fbelavenuto/msxsdmapperv2/CPLD/src/sdmapper.vhd

--
-- Projeto MSX SD Mapper
--
-- Copyright (c) 2014
-- Fabio Belavenuto

-- This documentation describes Open Hardware and is licensed under the CERN OHL v. 1.1.
-- You may redistribute and modify this documentation under the terms of the
-- CERN OHL v.1.1. (http://ohwr.org/cernohl). This documentation is distributed
-- WITHOUT ANY EXPRESS OR IMPLIED WARRANTY, INCLUDING OF MERCHANTABILITY,
-- SATISFACTORY QUALITY AND FITNESS FOR A PARTICULAR PURPOSE.
-- Please see the CERN OHL v.1.1 for applicable conditions

-- Modulo TOP - implementa o controle da Megarom ASCII16 para o Nextor
-- HW version 2 - dropped Megaram to add HW timer

library ieee;
use ieee.std_logic_1164.all;
use ieee.numeric_std.all;

entity sdmapper is
	port(
		clock_i			: in    std_logic;
		reset_n_i		: in    std_logic;
		sw_i				: in    std_logic_vector( 1 downto 0);
		-- BUS interface
		addr_bus_i		: in    std_logic_vector(15 downto 0);
		data_bus_io		: inout std_logic_vector( 7 downto 0);
		wr_n_i			: in    std_logic;
		rd_n_i			: in    std_logic;
		iorq_n_i			: in    std_logic;
		m1_n_i			: in    std_logic;
		sltsl_n_i		: in    std_logic;
		busdir_n_o		: out   std_logic;
		wait_n_o			: out   std_logic;
		-- ROM interface
		rom_a_o			: out   std_logic_vector(17 downto 14);
		rom_ce_n_o		: out   std_logic;
		rom_we_n_o		: out   std_logic;
		-- RAM interface
		ram_a_o			: out   std_logic_vector(18 downto 13);
		ram_cs_n_o		: out   std_logic;
		ram_we_n_o		: out   std_logic;
		-- SD card interface
		sd_cs_n_o		: out   std_logic_vector( 1 downto 0);
		sd_sclk_o		: out   std_logic;
		sd_mosi_o		: out   std_logic;
		sd_miso_i		: in    std_logic;
		sd_wp_i			: in    std_logic_vector( 1 downto 0);		-- 1 = Write protected
		sd_pres_n_i		: in    std_logic_vector( 1 downto 0)		-- 0 = SD Card present
	);

end entity;

architecture Behavioral of sdmapper is

	signal io_cs	  		: std_logic;
	signal iomapper_s		: std_logic;
	signal ffff				: std_logic;
	signal sltsl_c			: std_logic;
	signal slt_exp_n		: std_logic_vector(3 downto 0);
	signal sltsl_rom_n_s	: std_logic;
	signal sltsl_ram_n_s	: std_logic;
	signal wait_n_s		: std_logic;

	-- Regs
	signal regs_cs_s		: std_logic;

	-- SPI port
	signal spi_cs_s		: std_logic;
	signal sd_chg_q		: std_logic_vector(1 downto 0);
	signal sd_chg_s		: std_logic_vector(1 downto 0);
	signal status_s		: std_logic_vector(7 downto 0);
	signal spi_ctrl_wr_s	: std_logic;
	signal spi_ctrl_rd_s	: std_logic;
	signal sd_sel_q		: std_logic_vector(1 downto 0);

	-- Flash ASCII16
	signal rom_bank_wr_s	: std_logic;
	signal rom_bank1_q	: std_logic_vector(2 downto 0);
	signal rom_bank2_q	: std_logic_vector(3 downto 0);

	-- Timer
	signal tmr_cnt_q		: std_logic_vector(15 downto 0);	-- clock 25MHz: decrement each 40ns
	signal tmr_wr_s		: std_logic;
	signal tmr_rd_s		: std_logic;

begin

	-- Porta SPI
	portaspi: entity work.spi
	port map (
		clock_i			=> clock_i,
		reset_n_i		=> reset_n_i,
		-- CPU interface
		cs_i				=> spi_cs_s,
		data_bus_io		=> data_bus_io,
		wr_n_i			=> wr_n_i,
		rd_n_i			=> rd_n_i,
		wait_n_o			=> wait_n_s,
		-- SD card interface
		spi_sclk_o		=> sd_sclk_o,
		spi_mosi_o		=> sd_mosi_o,
		spi_miso_i		=> sd_miso_i
	);

	wait_n_o	<= 'Z'	when wait_n_s = '1'	else '0';

	-- Expansor de slot
	exp: entity work.exp_slot
	port map (
		reset_n		=> reset_n_i,
		sltsl_n		=> sltsl_c,
		cpu_rd_n		=> rd_n_i,
		cpu_wr_n		=> wr_n_i,
		ffff			=> ffff,
		cpu_a			=> addr_bus_i(15 downto 14),
		cpu_d			=> data_bus_io,
		exp_n			=> slt_exp_n
	);

	-- Mapper
	memmapper: entity work.mapper
	port map (
		reset_n_i	=> reset_n_i,
		cpu_a_i		=> addr_bus_i,
		cpu_d_io		=> data_bus_io,
		ioFx_i		=> iomapper_s,
		cpu_rd_n_i	=> rd_n_i,
		cpu_wr_n_i	=> wr_n_i,
		sltsl_n_i	=> sltsl_ram_n_s,
		sram_ma_o	=> ram_a_o,
		sram_cs_n_o	=> ram_cs_n_o,
		sram_we_n_o	=> ram_we_n_o,
		busdir_n_o	=> busdir_n_o
	);

	-- Glue Logic

	-- Enable portas I/O
	io_cs			<= not iorq_n_i and m1_n_i and sw_i(0);

	-- Slot expander address select
	ffff    <= '1' when addr_bus_i = X"FFFF" else '0';

	-- Slot Selects
	sltsl_c			<= sltsl_n_i    when sw_i(0) = '1' else '1';
	sltsl_rom_n_s	<= slt_exp_n(0) when sw_i(0) = '1' else sltsl_n_i;
	sltsl_ram_n_s	<= slt_exp_n(1) when sw_i(0) = '1' else '1';

	iomapper_s	<= '1' when io_cs = '1' and addr_bus_i(7 downto 2) = "111111"				else '0';	-- Acesso I/O portas $FC a $FF

	-- Status flags
	-- If no SD card is selected:
	-- b7-b2 : always 0
	-- b1-b0 : Switches status
	--
	-- If any SD card is selected:
	-- b7-b3 : always 0
	-- b2 : 1=Write protecton enabled for SD card slot selected
	-- b1 : 0=SD card present on slot selected
	-- b0 : 1=SD Card on slot selected changed since last read
	status_s	<= "000000" & sw_i													when sd_sel_q = "00"	else		-- No SD selected
					"00000" & sd_wp_i(0) & sd_pres_n_i(0) & sd_chg_s(0)	when sd_sel_q = "01"	else		-- SD 1 selected
					"00000" & sd_wp_i(1) & sd_pres_n_i(1) & sd_chg_s(1)	when sd_sel_q = "10"	else		-- SD 2 selected
					(others => '-');

	-- Megarom ASCII16
	-- 6000 = 011 00...
	-- 6800 = 011 01...
	-- 7000 = 011 10...
	-- 7800 = 011 11...

	rom_bank_wr_s <= 
		'1' when sltsl_rom_n_s = '0' and wr_n_i = '0' and addr_bus_i(15 downto 13) = "011" and addr_bus_i(11) = '0'	else
		'0';

	-- Bank write
	process (reset_n_i, rom_bank_wr_s)
	begin
		if reset_n_i = '0' then
			rom_bank1_q		<= (others => '0');
			rom_bank2_q		<= (others => '0');
		elsif falling_edge(rom_bank_wr_s) then
			case addr_bus_i(12) is
				when '0'   =>
					rom_bank1_q		<= data_bus_io(2 downto 0);
				when '1'   =>
					rom_bank2_q		<= data_bus_io(3 downto 0);
				when others =>
					null;
			end case;
		end if;
	end process;

	-- Flash control
	rom_a_o(17)	<= sw_i(1);
	rom_a_o(16 downto 14) <= 
		rom_bank1_q 				when addr_bus_i(15 downto 14) = "01" and sltsl_rom_n_s = '0'	else
		rom_bank2_q(2 downto 0)	when addr_bus_i(15 downto 14) = "10" and sltsl_rom_n_s = '0'	else
		(others => '-');

	-- Flash /CS control
	rom_ce_n_o <=
		-- Excludes SPI range and regs range
		'0'	when addr_bus_i(15 downto 14) = "01" and sltsl_rom_n_s = '0' and rd_n_i = '0'	and spi_cs_s = '0' and regs_cs_s = '0'	else
		'0'	when addr_bus_i(15 downto 14) = "10" and sltsl_rom_n_s = '0' and rom_bank2_q(3) = '1'					else		-- Only if bank > 7
		'1';

	-- Flash /WE control
	rom_we_n_o	<=	'0'	when addr_bus_i(15 downto 14) = "10" and sltsl_rom_n_s = '0' and wr_n_i = '0'	else
						'1';

	regs_cs_s <= '1'	when	sltsl_rom_n_s = '0' and addr_bus_i >= X"7FF0"  	else '0';

	-- Disk change FFs
	process (reset_n_i, spi_ctrl_rd_s, sd_sel_q, sd_pres_n_i(0))
	begin
		if reset_n_i = '0' then
			sd_chg_q(0) <= '0';
		elsif sd_pres_n_i(0) = '1' then
			sd_chg_q(0) <= '1';
		elsif falling_edge(spi_ctrl_rd_s) then
			if sd_sel_q = "01" then
				sd_chg_q(0) <= '0';
			end if;
		end if;
	end process;

	process (reset_n_i, spi_ctrl_rd_s, sd_sel_q, sd_pres_n_i(1))
	begin
		if reset_n_i = '0' then
			sd_chg_q(1) <= '0';
		elsif sd_pres_n_i(1) = '1' then
			sd_chg_q(1) <= '1';
		elsif falling_edge(spi_ctrl_rd_s) then
			if sd_sel_q = "10" then
				sd_chg_q(1) <= '0';
			end if;
		end if;
	end process;

	process (reset_n_i, spi_ctrl_rd_s)
	begin
		if reset_n_i = '0' then
			sd_chg_s <= (others => '0');
		elsif rising_edge(spi_ctrl_rd_s) then
			sd_chg_s <= sd_chg_q;
		end if;
	end process;

	-- SPI
	spi_ctrl_wr_s <= '1' when sltsl_rom_n_s = '0' and wr_n_i = '0' and addr_bus_i = X"7FF0"	else '0';
	spi_ctrl_rd_s <= '1' when sltsl_rom_n_s = '0' and rd_n_i = '0' and addr_bus_i = X"7FF0"	else '0';

	-- SPI Control register write
	process (reset_n_i, spi_ctrl_wr_s)
	begin
		if reset_n_i = '0' then
			sd_sel_q		<= "00";
		elsif falling_edge(spi_ctrl_wr_s) then
			sd_sel_q		<= data_bus_io(1 downto 0);
		end if;
	end process;

--	sd_cs_n_o	<= "10"	when sd_sel_q = "01"	else		-- SD 1 selected
--						"01"	when sd_sel_q = "10"	else		-- SD 2 selected
--						"11";
	sd_cs_n_o <= not sd_sel_q;

	-- 7B00 = 0111 1011
	-- 7F00 = 0111 1111
	spi_cs_s	<= '1'  when	sltsl_rom_n_s = '0' and rom_bank1_q = "111" and	addr_bus_i >= X"7B00" and addr_bus_i < X"7F00"   else
	            '0';

	-- Timer
	process (clock_i)
	begin
		if rising_edge(clock_i) then
			if tmr_wr_s = '1' then
				tmr_cnt_q(15 downto 8) <= data_bus_io;
				tmr_cnt_q( 7 downto 0) <= (others => '1');
			elsif tmr_cnt_q /= 0 then
				tmr_cnt_q <= tmr_cnt_q - 1;
			end if;
		end if;
	end process;

	tmr_wr_s <= '1' when sltsl_rom_n_s = '0' and wr_n_i = '0' and addr_bus_i = X"7FF1"	else '0';
	tmr_rd_s <= '1' when sltsl_rom_n_s = '0' and rd_n_i = '0' and addr_bus_i = X"7FF1"	else '0';

	-- Bus
	data_bus_io	<= status_s	when spi_ctrl_rd_s = '1'	else
						tmr_cnt_q(15 downto 8)	when tmr_rd_s = '1' 			else		-- 40ns * 256 = 10240 ns
						(others => 'Z');

end Behavioral;
